DanielOlivaRodriguez/TFG-Daniel-Oliva/Imágenes/ecg.png

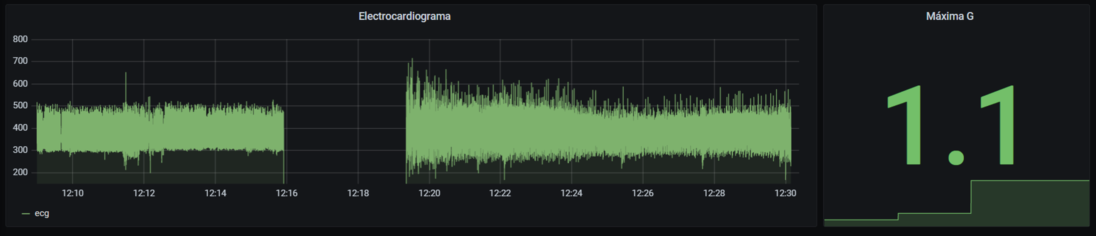
Imágenes/ecg.png
