DanielOlivaRodriguez/TFG-Daniel-Oliva/Imágenes/saturación.png

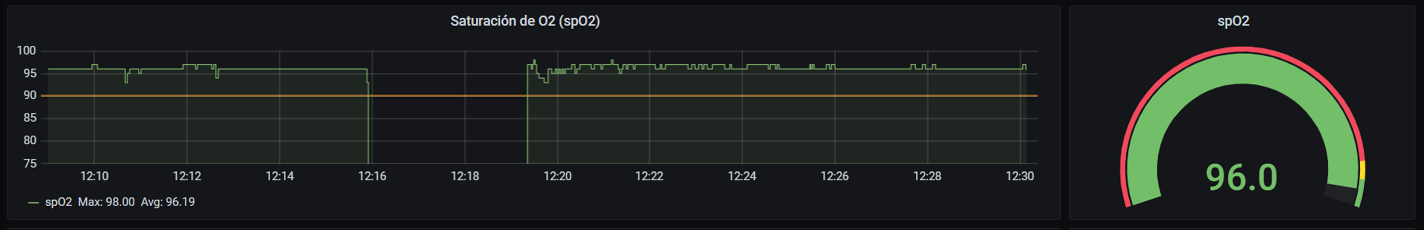
Imágenes/saturación.png
