DanielOlivaRodriguez/TFG-Daniel-Oliva/Imágenes/temperatura.png

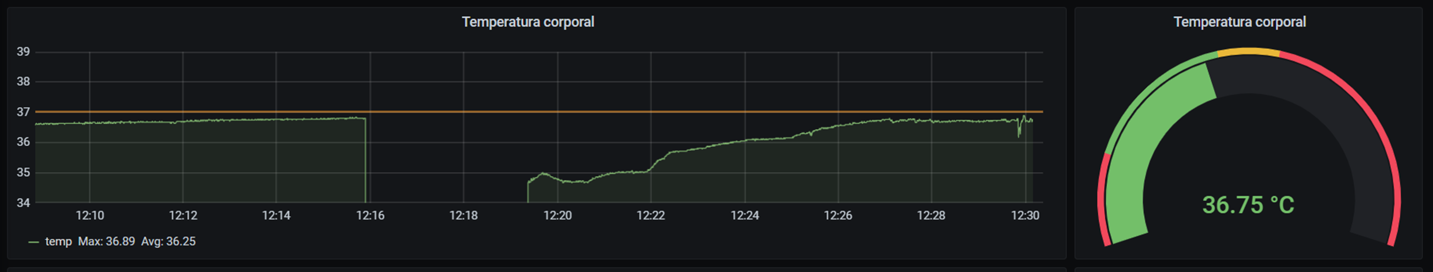
Imágenes/temperatura.png
